abrahanlp/Home-Ambient/Hardware/Docu/SEPIC.asc

C1: cap; 50n
C2: cap; 10µ
D1: diode
L1: ind; 33µ; Rser=1m
L2: ind; 33µ; Rser=1m
R1: res; 13
S1: sw; MySwitch
V1: voltage; 3V
V2: voltage; PULSE(0 2 0 1n 1n 600n 1u)
Named nets: 0, Vsw, Vout, Vin
.tran 0 1000u 0
.model MySwitch SW(Ron=.350 Roff=1Meg Vt=1 Vh=-.5)
