abrahanlp/Home-Ambient/Hardware/SimuComparator/ComparatorEquivalent.asc

R1: res; {R1}
R2: res; {R2}
R3: res; {Rf}
R4: res; {R1}
R5: res; {R1}
R6: res; {R2}
R7: res; {Rf}
R8: res; {R1}
V1: voltage; 1
Vol: voltage; .2
Named nets: 0, Vsys, VinH, VinL
.param R1=148k R2=100k Rf=3.5Meg
.dc V1 2.8 3.2 5m
